snurrebassen/eclipse/plates/STEP/STEP previews/ISO_updated.png

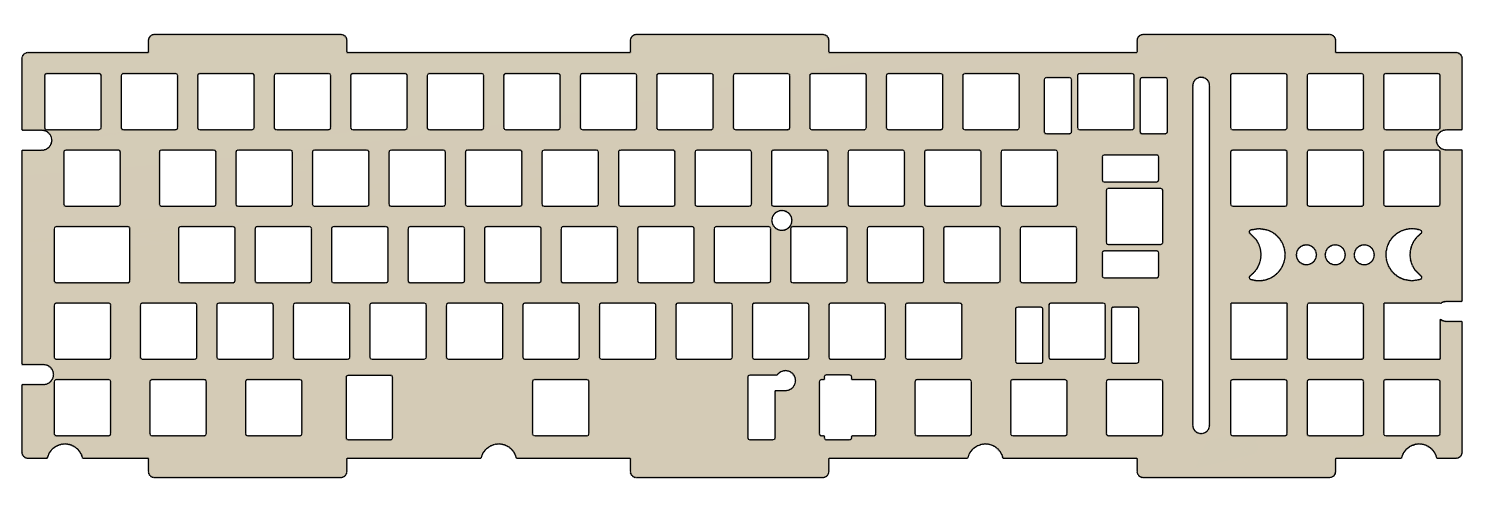
plates/STEP/STEP previews/ISO_updated.png
